calble/Weather-Station/wmath.h

#ifndef WMATH
#define WMATH

float cToF(float c);
float minValue(float arr[], int offset, int count);
float maxValue(float arr[], int offset, int count);
int minValue(int arr[], int offset, int count);
int maxValue(int arr[], int offset, int count);
float range(float arr[], int hour);
float smallest(float arr[], int hour);
float largest(float arr[], int hour);

void replaceStr(char* str, char org, char replace);
#endif
